GreenHamr/PRAVETZ-8D-Oric-Atmos/STL/PRAVETZ-8D/PRAVETZ-8D - keyboard.stl

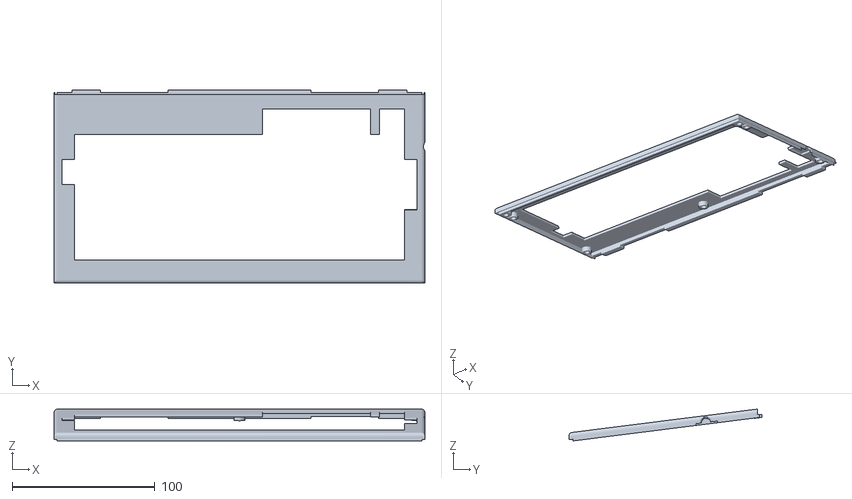
[picture p24: CAD file, 2024-12-23]
STL/PRAVETZ-8D/PRAVETZ-8D - keyboard.stl
260.0 x 135.5 x 22.3
