GreenHamr/PRAVETZ-8D-Oric-Atmos/STL/PRAVETZ-8D/PRAVETZ-8D - base.stl

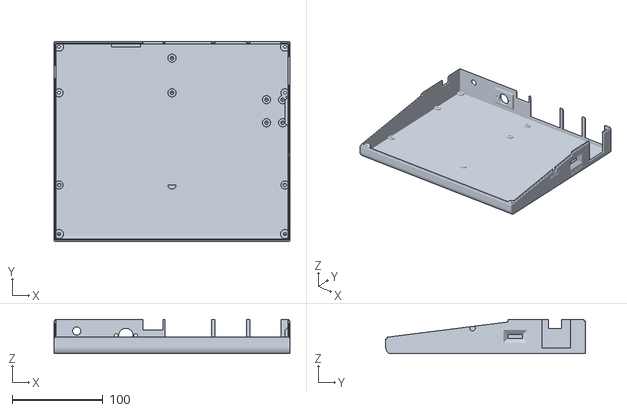
[picture p25: CAD file, 2024-12-23]
STL/PRAVETZ-8D/PRAVETZ-8D - base.stl
260.0 x 220.0 x 38.0
