GreenHamr/PRAVETZ-8D-Oric-Atmos/STL/PRAVETZ-8D/PRAVETZ-8D - FDD_support.stl

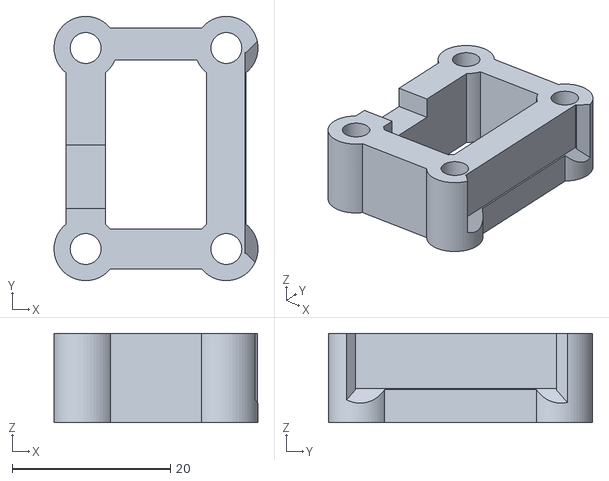
[picture p26: CAD file, 2024-12-20]
STL/PRAVETZ-8D/PRAVETZ-8D - FDD_support.stl
25.8 x 33.4 x 11.3
