GreenHamr/PRAVETZ-8D-Oric-Atmos/firmware/IO_Expander_Logic/eprom_floppy_content.hpp

#ifndef EPROM_FLOPPTY_C_H_
#define EPROM_FLOPPTY_C_H_

#define FLOPPY_ROM_SIZE 2048


uint8_t FLOPPY_ROM_MEMORY[FLOPPY_ROM_SIZE] = {
0xFF,0xFF,0xFF,0xFF,0xFF,0xFF,0xFF,0xFF,0xFF,0xFF,0xFF,0xFF,0xFF,0xFF,0xFF,0xFF,
0xFF,0xFF,0xFF,0xFF,0xFF,0xFF,0xFF,0xFF,0xFF,0xFF,0xFF,0xFF,0xFF,0xFF,0xFF,0xFF,
0x78,0xA2,0x05,0xBD,0x2F,0x03,0x9D,0xEA,0x02,0xCA,0x10,0xF7,0x4C,0xEA,0x02,0x8D,
0x82,0x03,0x4C,0x20,0x03,0x42,0x4F,0x42,0x59,0xFF,0xFF,0x8D,0x81,0x03,0x20,0x03,
0xD4,0x8D,0x80,0x03,0x60,0x8D,0x81,0x03,0x20,0x06,0xD4,0x8D,0x80,0x03,0x60,0x8D,
0x80,0x03,0x20,0x5F,0xC5,0x8D,0x81,0x03,0x60,0x8D,0x80,0x03,0x20,0xC5,0xE0,0x8D,
0x81,0x03,0x60,0x8D,0x80,0x03,0x4C,0xBD,0xC4,0x78,0x8D,0x81,0x03,0x20,0x00,0xD4,
0x8D,0x80,0x03,0x58,0x4C,0x03,0xC0,0x78,0x8D,0x81,0x03,0x4C,0x00,0xC0,0x8D,0x80,
0x03,0x20,0x92,0xC5,0x8D,0x81,0x03,0x60,0x8D,0x80,0x03,0x20,0xFB,0xCC,0x8D,0x81,
0x03,0x60,0x8D,0x80,0x03,0x20,0xA0,0x03,0x8D,0x81,0x03,0x40,0x20,0xA0,0x03,0x40,
0x08,0x48,0xA9,0x03,0x48,0xA9,0xAC,0x48,0x08,0x4C,0x22,0xEE,0x68,0x28,0x60,0xFF,
0xFF,0xFF,0xFF,0xFF,0xFF,0xFF,0xFF,0xFF,0xFF,0xFF,0xFF,0xFF,0xFF,0xFF,0xFF,0xFF,
0x04,0x02,0x0F,0xFF,0xFF,0xFF,0xFF,0xFF,0xFF,0xFF,0xFF,0xFF,0xFF,0xFF,0xFF,0xFF,
0xFF,0xFF,0xFF,0xFF,0xFF,0xFF,0xFF,0xFF,0xFF,0xFF,0xFF,0xFF,0xFF,0xFF,0xFF,0xFF,
0xFF,0xFF,0xFF,0xFF,0xFF,0xFF,0xFF,0xFF,0xFF,0xFF,0xFF,0xFF,0xFF,0xFF,0xFF,0xFF,
0xFF,0xFF,0xFF,0xFF,0xFF,0xFF,0xFF,0xFF,0xFF,0xFF,0xFF,0xFF,0xFF,0xFF,0xFF,0xFF,

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
0xFF,0xFF,0xFF,0xFF,0xFF,0xFF,0xFF,0xFF,0xFF,0xFF,0xFF,0xFF,0xFF,0xFF,0xFF,0xFF,
0xFF,0xFF,0xFF,0xFF,0xFF,0xFF,0xFF,0xFF,0xFF,0xFF,0xFF,0xFF,0xFF,0xFF,0xFF,0xFF,
0xFF,0xFF,0xFF,0xFF,0xFF,0xFF,0xFF,0xFF,0xFF,0xFF,0xFF,0xFF,0xFF,0xFF,0xFF,0xFF,
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
}; 



#endif
